pgatti86/smart-epd/components/page_manager/include/epd_images.h

#ifndef __EPD_IMAGES_H__
#define __EPD_IMAGES_H__

//note: const data are keep in FLASH memory

//'ic_drop' 24x24
const unsigned char DROP_IMAGE_DATA[] = {
/* 0X00,0X01,0X80,0X00,0X28,0X01, */
0xff, 0xff, 0xff, 0xff, 0xff, 0xff, 0xff, 0xff, 0xff, 0xff, 0xff, 0xff, 0xf8, 0x0f, 0xff, 0xe0, 
0x07, 0xff, 0xc0, 0x01, 0xff, 0xc3, 0x80, 0x7f, 0x8e, 0x00, 0x3f, 0x8c, 0x00, 0x0f, 0x18, 0x00, 
0x01, 0x18, 0x00, 0x00, 0x00, 0x00, 0x00, 0x00, 0x00, 0x01, 0x80, 0x00, 0x0f, 0x80, 0x00, 0x3f, 
0xc0, 0x00, 0x7f, 0xc0, 0x01, 0xff, 0xe0, 0x07, 0xff, 0xf8, 0x0f, 0xff, 0xff, 0xff, 0xff, 0xff, 
0xff, 0xff, 0xff, 0xff, 0xff, 0xff, 0xff, 0xff, 
};

// 'ic_termometer', 24x24px
const unsigned char TEMP_IMAGE_DATA[] = {
/* 0X00,0X01,0X80,0X00,0X28,0X01, */
0xff, 0xff, 0xff, 0xff, 0xff, 0xff, 0xff, 0xff, 0xff, 0xff, 0xff, 0xff, 0xff, 0xff, 0xff, 0xff, 
0xff, 0xff, 0xf0, 0xff, 0xff, 0xc0, 0x3f, 0xff, 0x86, 0x00, 0x03, 0x99, 0x80, 0x01, 0x10, 0x7f, 
0xf8, 0x20, 0x00, 0x3c, 0x20, 0x00, 0x3c, 0x10, 0x7f, 0xf8, 0x99, 0x80, 0x01, 0x86, 0x00, 0x03, 
0xc0, 0x3f, 0xff, 0xf0, 0xff, 0xff, 0xff, 0xff, 0xff, 0xff, 0xff, 0xff, 0xff, 0xff, 0xff, 0xff, 
0xff, 0xff, 0xff, 0xff, 0xff, 0xff, 0xff, 0xff
};

// 'ic_wifi', 16x16px
const unsigned char WIFI_IMAGE_DATA[] = {
/* 0X00,0X01,0X80,0X00,0X28,0X01, */
0xff, 0xdf, 0xff, 0x9f, 0xff, 0xcf, 0xfe, 0xc7, 0xfc, 0xe7, 0xfe, 0x67, 0xf6, 0x67, 0xe6, 0x73, 
0xe6, 0x73, 0xf6, 0x67, 0xfe, 0x67, 0xfc, 0xe7, 0xfe, 0xc7, 0xff, 0xcf, 0xff, 0x9f, 0xff, 0xdf
};

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
0xff, 0xff, 0xff, 0xff, 0xf8, 0x1f, 0xff, 0xff, 0xff, 0xff, 0xf8, 0x1f, 0xff, 0xff, 0xff, 0xff, 
0xfc, 0x3f, 0xff, 0xff, 0xff, 0xff, 0xfc, 0x3f, 0xff, 0xff, 0xff, 0xff, 0xfe, 0x7f, 0xff, 0xff
};

#endif // __EPD_IMAGES_H__
