pgatti86/smart-epd/components/storage_manager/include/storage_manager.h

/*
 * storage_manager.h
 *
 *  Created on: May 28, 2019
 *      Author: paolo
 */

#ifndef COMPONENTS_STORAGE_MANAGER_INCLUDE_STORAGE_MANAGER_H_
#define COMPONENTS_STORAGE_MANAGER_INCLUDE_STORAGE_MANAGER_H_

#define ENROLLMENT_NOT_COMPLETED 0
#define ENROLLMENT_COMPLETED 1

void storage_manager_init();

int storage_manager_get_weather_zip_code();

void storage_manager_set_weather_zip_code(int zip_code);

char* storage_manager_get_weather_api_key();

void storage_manager_set_weather_api_key(char *api_key);

int storage_manager_get_enrollment_status();

bool storage_manager_has_enrollment_done();

void storage_manager_set_enrollment_status(int status);

void storage_manager_close_nvs();

void storage_manager_format_nvs();

char* storage_manager_get_device_config_from_spiffs();

char* storage_manager_get_ca_cert_from_spiffs();

char* storage_manager_get_device_cert_from_spiffs();

char* storage_manager_get_device_key_from_spiffs();

char* storage_manager_get_ota_cert_from_spiffs();

#endif
